wildjames/smart_compass/firmware/smart_compass_rs/src/handlers/dummy_handlers.rs

// UART
struct LC86LGNSS {}

// I2C
struct BNO085IMU {}

// Fuel Gauge is also I2C
// I2C
struct HapticMotor {}

// SPI
struct WioE5LoRa {}

// SPI
struct FlashMemory {}

// SPI
struct EInkDisplay {}

// GPIO
struct NeopixelChain {}

// GPIO
struct Button {}

// Internal
struct Bluetooth {}
